amead77/SCAD-gridfinity_rebuilt_ruler/IMG_0652.JPEG

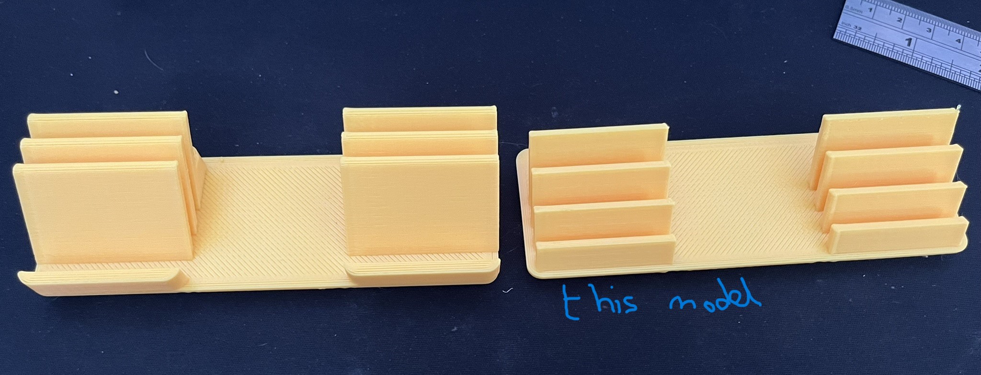
IMG_0652.JPEG
