amead77/SCAD-gridfinity_rebuilt_ruler/IMG_0653.JPEG

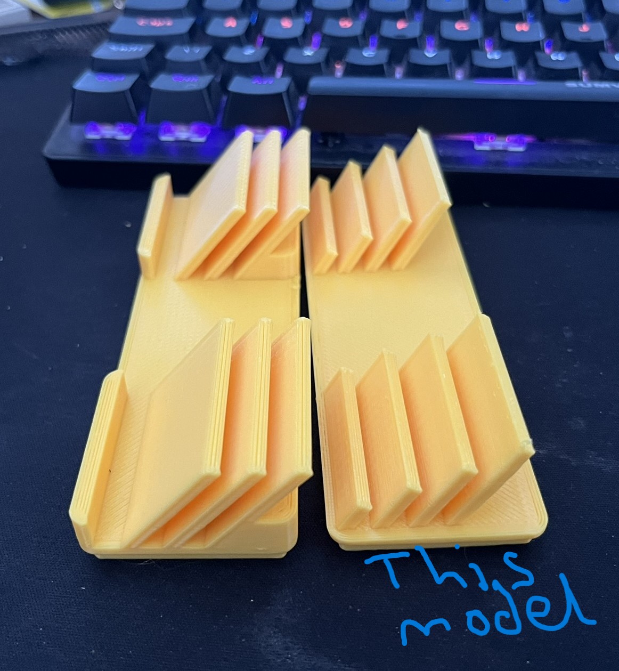
IMG_0653.JPEG
